waagsociety/holu-kit-20/Forum_images/HoLu_79_raw_data_ttn.png

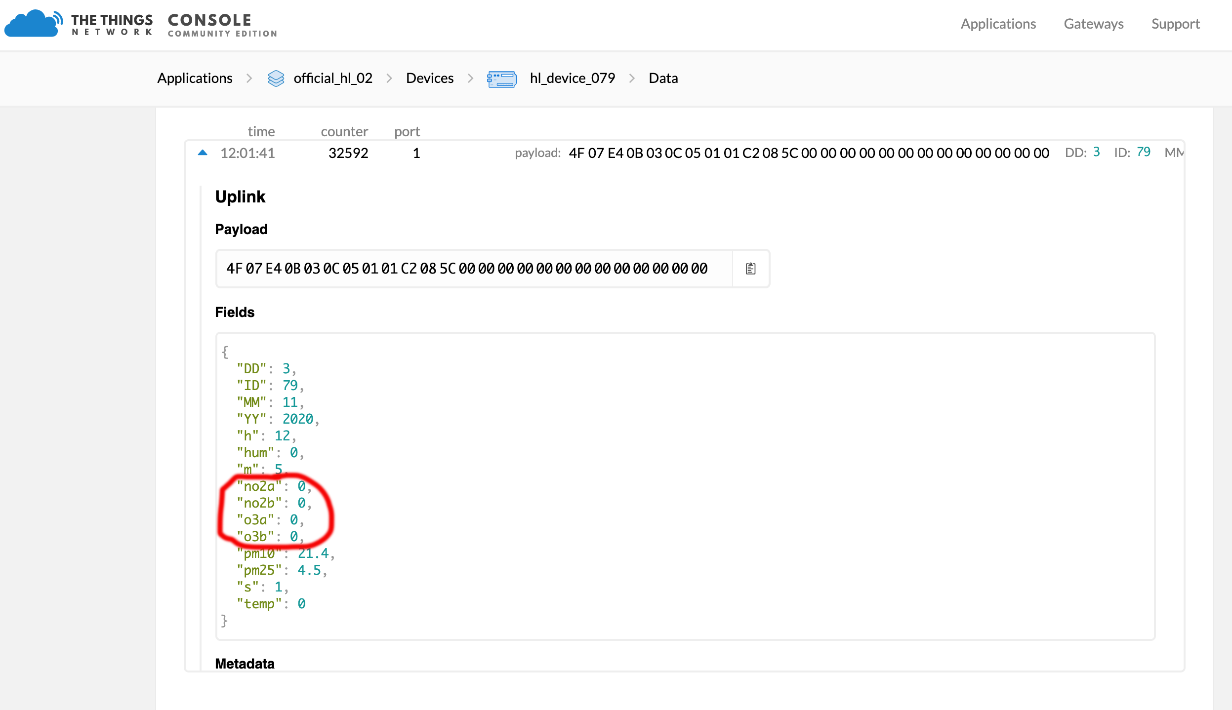
Forum_images/HoLu_79_raw_data_ttn.png
