waagsociety/holu-kit-20/Forum_images/HoLu_191_193_no2b_Oct12.png

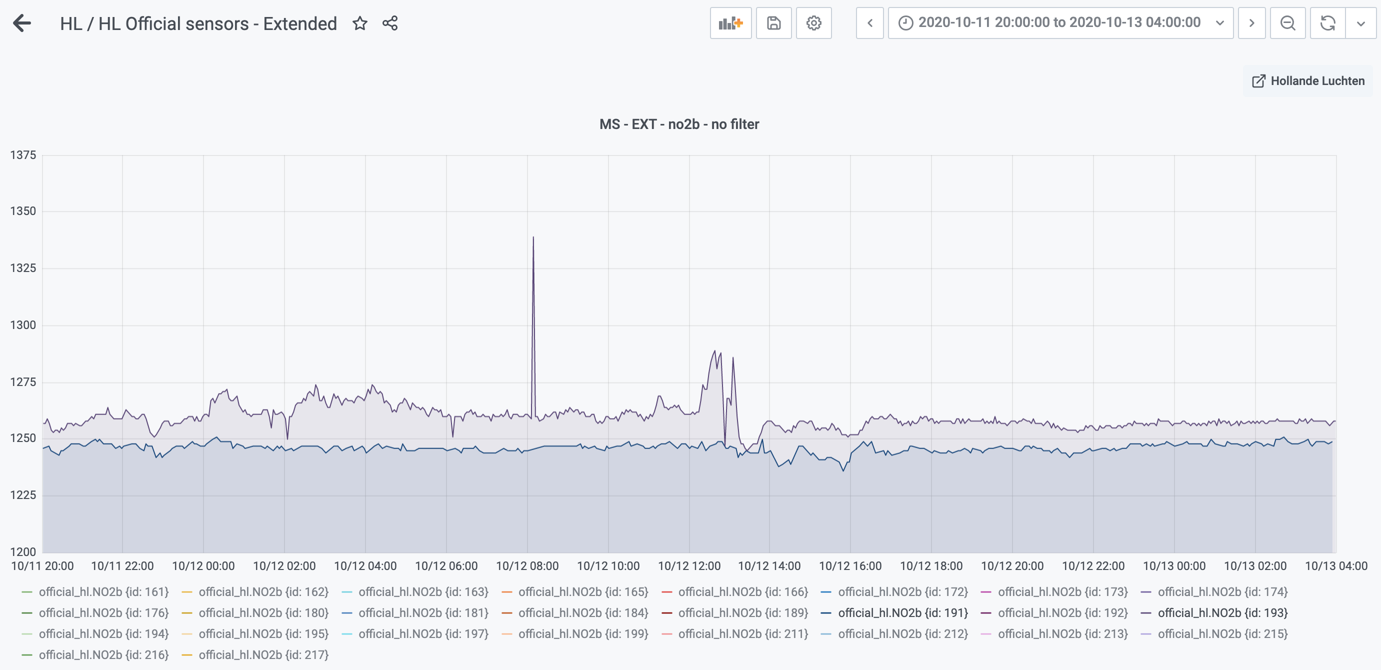
Forum_images/HoLu_191_193_no2b_Oct12.png
