waagsociety/holu-kit-20/Internal Hardware/images/HL_bme_bottom_popluated_photo.jpg

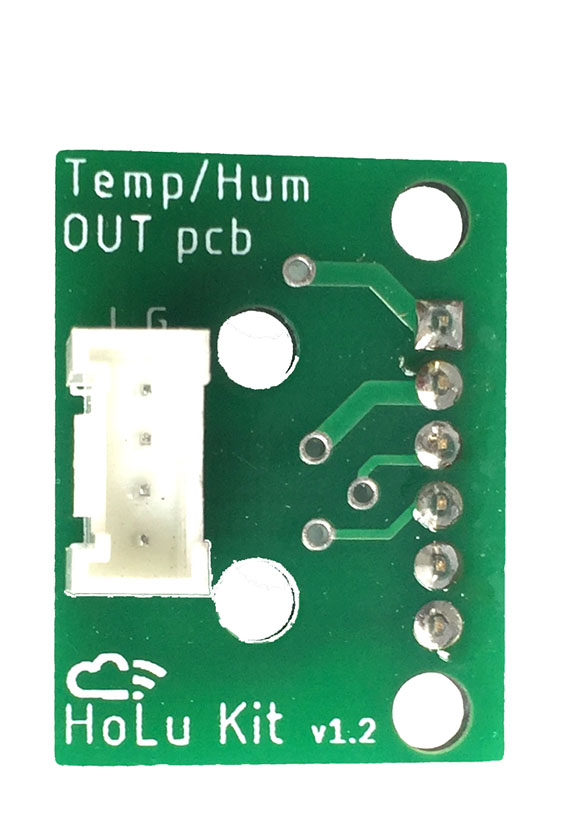
Internal Hardware/images/HL_bme_bottom_popluated_photo.jpg
