waagsociety/holu-kit-20/Software/HL_main_extended/data/Anatomical_theatre_Leiden.jpg

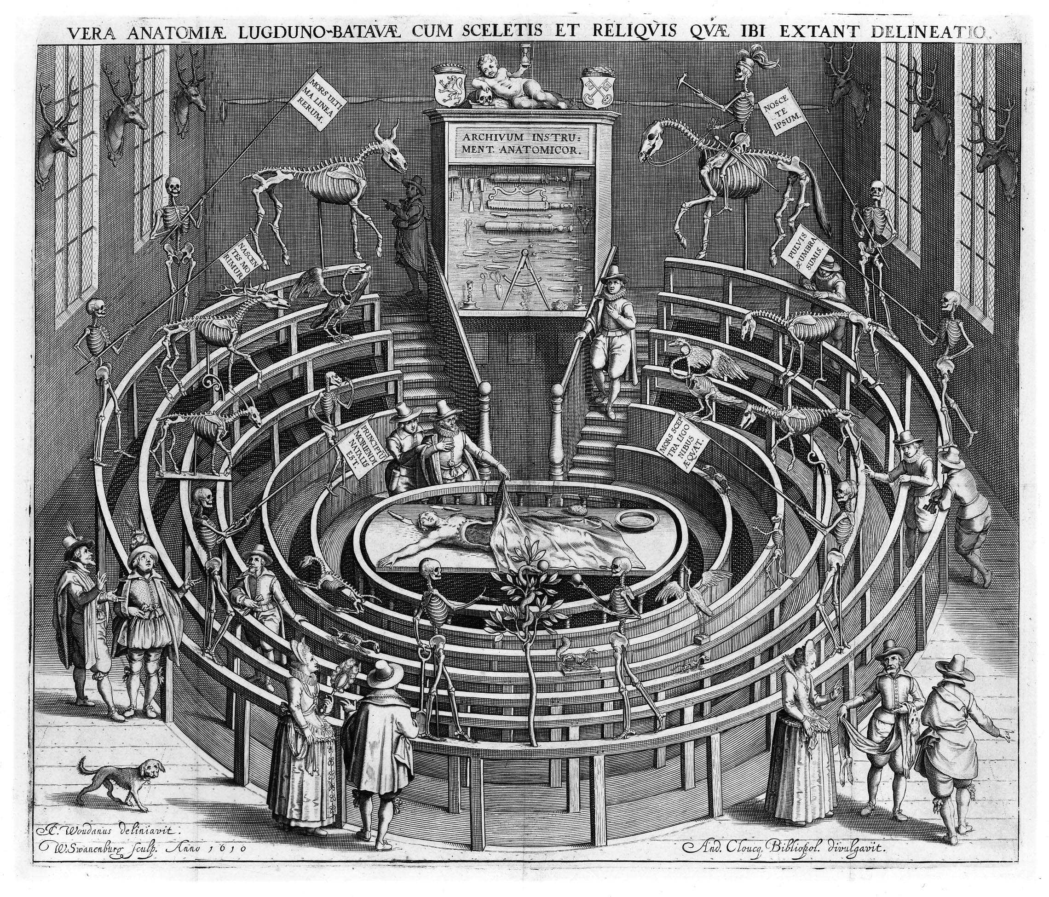
Software/HL_main_extended/data/Anatomical_theatre_Leiden.jpg
